The-Automation-Warehouse/1D-Ball-Balancer/making of/Probing.jpg

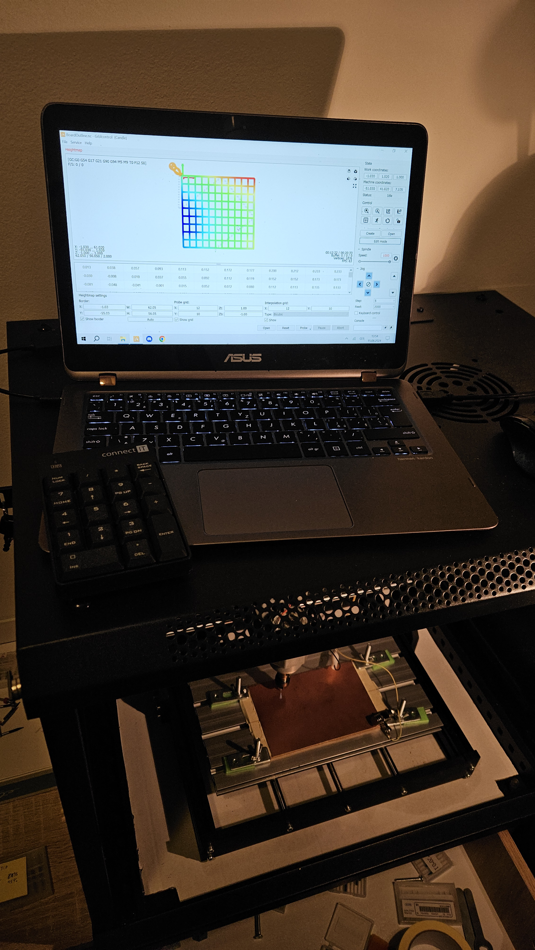
making of/Probing.jpg
