The-Automation-Warehouse/1D-Ball-Balancer/making of/Soldering prep.jpg

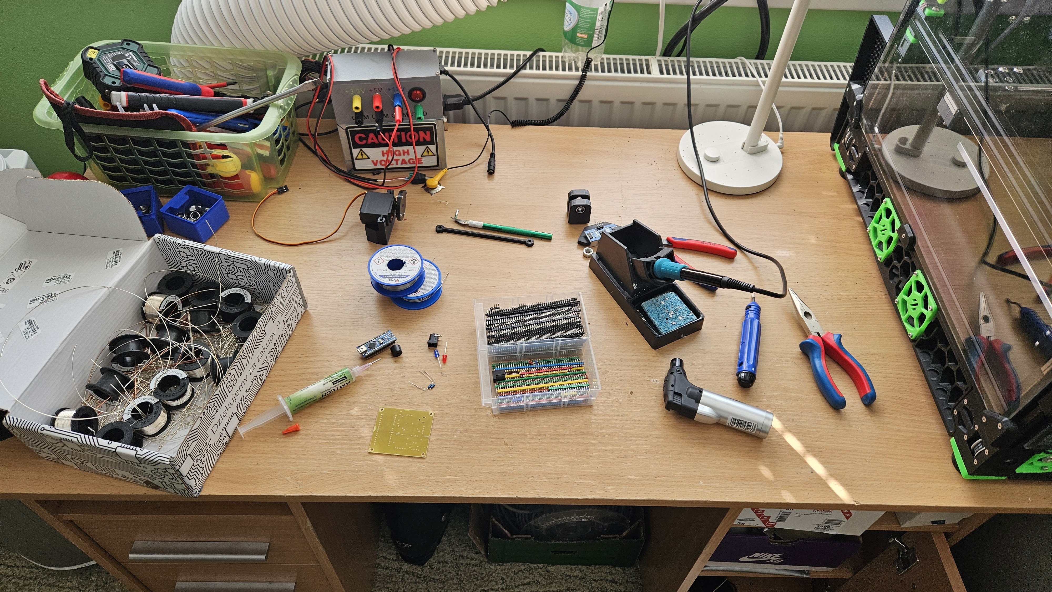
making of/Soldering prep.jpg
