The-Automation-Warehouse/1D-Ball-Balancer/making of/debugging.jpg

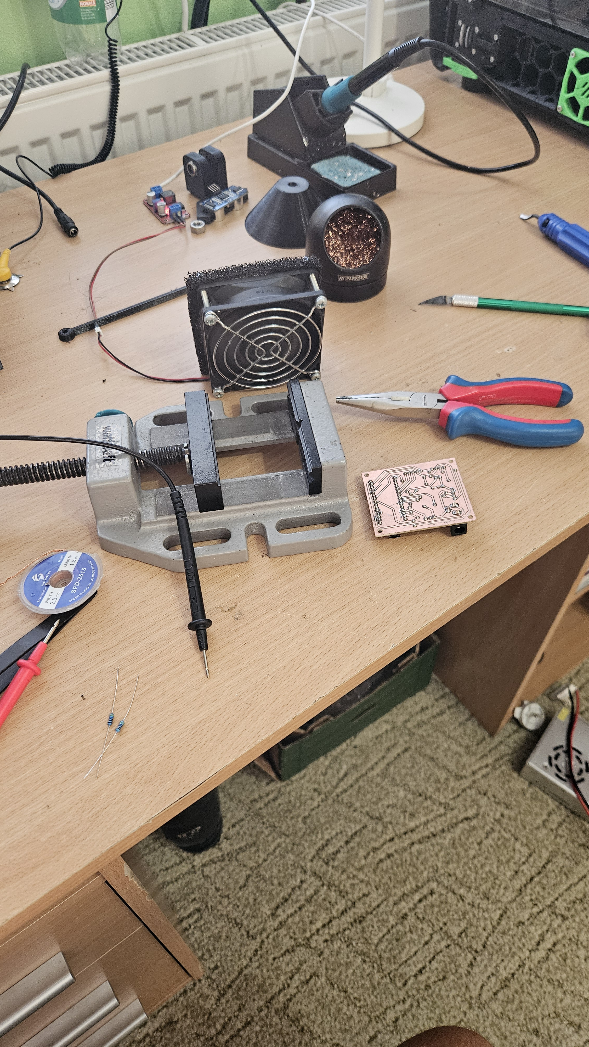
making of/debugging.jpg
